austinscreations/Button-panel/code/v3_MQTT_wifi_type_1_buttons/buttons.cpp

/*
 * buttons.cpp
 * 
 * A push button Arduino library capable of returning the number of
 * consecutive button presses made in quick succession or if the 
 * button was held down for a long time. 
 * 
 * Based on LSC_Button by ben.jones12@gmail.com, forked from mdButton library
 * Based on mdPushButton by Michel Deslierres <sigmdel.ca/michel>
 * 
 */

#include "Arduino.h"
#include "buttons.h"

#define VERSION 0x0004

// If active = LOW (the default) then the input must be pulled high most of the time
//   This can be done with the internal pullup (set pullup = true which is also the default value) 
//   or an external pull up resistor say 4.7K + connected to the  GPIO pin and Vcc
//
// If active = HIGH then the input must be pulled low most of the time
//   This can be done with the internal pulldown (set pullup = true which is also the default value) 
//   or an external pull down resistor say 4.7K + connected to the  GPIO pin and Vcc

multiButton::multiButton(){}

void multiButton::setup(uint8_t id, uint8_t pin, uint8_t active, bool useInternalPullResistor) {

  _pin[id] = pin;
  _active[id] = active;

  int mode = INPUT;
  if (useInternalPullResistor) {
    if (active == LOW)
      mode = INPUT_PULLUP;
    else {
      // mode = INPUT_PULLDOWN where defined
      #if defined(INPUT_PULLDOWN) 
        mode = INPUT_PULLDOWN;
      #elif defined(ESP8266)
        if (pin == 16) mode = INPUT_PULLDOWN_16;
      #endif 
    }
    _BUTTON_COUNT = _BUTTON_COUNT + 1;
//    Serial.println(_BUTTON_COUNT);
  }

   pinMode(_pin[id], mode);
  _buttonState[id].data.state = AWAIT_PRESS;
}


void multiButton::onButtonPressed(buttonPressedCallback callback)
{ 
  _onButtonPressed = callback; 
}


void multiButton::process() 
{

  // Process each input to see what, if any, events have occured
  uint8_t * state = _update();

  // Check if we have a callback to handle the press events
  if (_onButtonPressed) 
  {
    for (uint8_t i = 0; i < _BUTTON_COUNT; i++)
    {
      // Only interested in buttons with events to report
      if (state[i] != BUTTON_NO_STATE) {
//        Serial.println(state);
        _onButtonPressed(i, state[i]);
      }
    }
  }
}


uint8_t * multiButton::_update()
{
   static uint8_t state[BUTTON_COUNT_MAX] = {};
  
  // Work out how long since our last update so we can increment the event times for each button
  uint16_t delta = millis() - _lastUpdateTime;
  _lastUpdateTime = millis();

   for (uint8_t id = 0; id < _BUTTON_COUNT; id++)
  {
    state[id] = BUTTON_NO_STATE;
  
    // Increment the event time for this button
    _eventTime[id] = _eventTime[id] + delta;
    
    // AWAIT_PRESS
    if (_buttonState[id].data.state == AWAIT_PRESS) 
    {
      _buttonState[id].data.clicks = 0;
      if (digitalRead(_pin[id]) == _active[id])
      {
        _buttonState[id].data.state = DEBOUNCE_PRESS;
        _eventTime[id] = 0;
      }
    }
    // DEBOUNCE_PRESS
    else if (_buttonState[id].data.state == DEBOUNCE_PRESS) 
    {
      if (_eventTime[id] > DEBOUNCE_PRESS_TIME) 
      {
        _buttonState[id].data.state = AWAIT_RELEASE;
        _eventTime[id] = 0;
      }
    }
    // AWAIT_RELEASE
    else if (_buttonState[id].data.state == AWAIT_RELEASE) 
    {
      if (!(digitalRead(_pin[id]) == _active[id])) 
      {
        _buttonState[id].data.state = DEBOUNCE_RELEASE;
        _eventTime[id] = 0;
      }
      else
      {
        if (_eventTime[id] > HOLD_TIME)
        {
          _buttonState[id].data.clicks = BUTTON_HOLD_STATE ;
          _eventTime[id] = 0;
          state[id] = BUTTON_HOLD_STATE;
        }
      }
    }
    // DEBOUNCE_RELEASE
    else if (_buttonState[id].data.state == DEBOUNCE_RELEASE) 
    {
      if (_eventTime[id] > DEBOUNCE_RELEASE_TIME) 
      {
        if (_buttonState[id].data.clicks == BUTTON_HOLD_STATE ) 
        {
          _buttonState[id].data.state = AWAIT_PRESS;
           state[id] = 0;
        }
        else
        {
          _buttonState[id].data.clicks = min(BUTTON_MAX_CLICKS, _buttonState[id].data.clicks + 1);
          _buttonState[id].data.state = AWAIT_MULTI_PRESS;
          _eventTime[id] = 0; 
        }
       }
      }
    
    // AWAIT_MULTI_PRESS
    else if (_buttonState[id].data.state == AWAIT_MULTI_PRESS) 
    { 
      if (digitalRead(_pin[id]) == _active[id])
      {
        _buttonState[id].data.state = DEBOUNCE_PRESS;
        _eventTime[id] = 0;
      } 
      else if (_eventTime[id] > MULTI_CLICK_TIME) 
      {
        _buttonState[id].data.state = AWAIT_PRESS;
        state[id] = _buttonState[id].data.clicks;
      }
    }
  }
  
    return state;
}
